VCRchitect/OneTrolla/KiCad Files/3D Models/ss12d00-1.snapshot.10/SS12D00 view 1.jpg

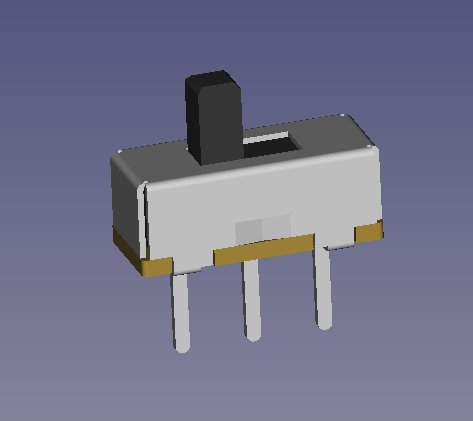
KiCad Files/3D Models/ss12d00-1.snapshot.10/SS12D00 view 1.jpg
